BleepSound/ms20-vcf-simple/documentation/image/MS20-VCF-3D_bottom.png

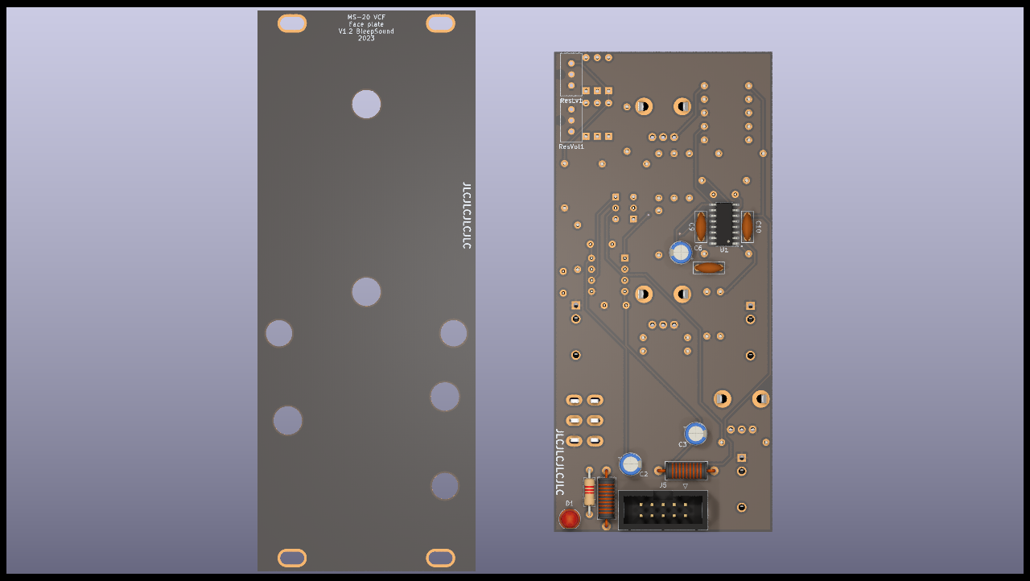
documentation/image/MS20-VCF-3D_bottom.png
