BleepSound/ms20-vcf-simple/documentation/image/MS20-VCF-3D_top30deg.png

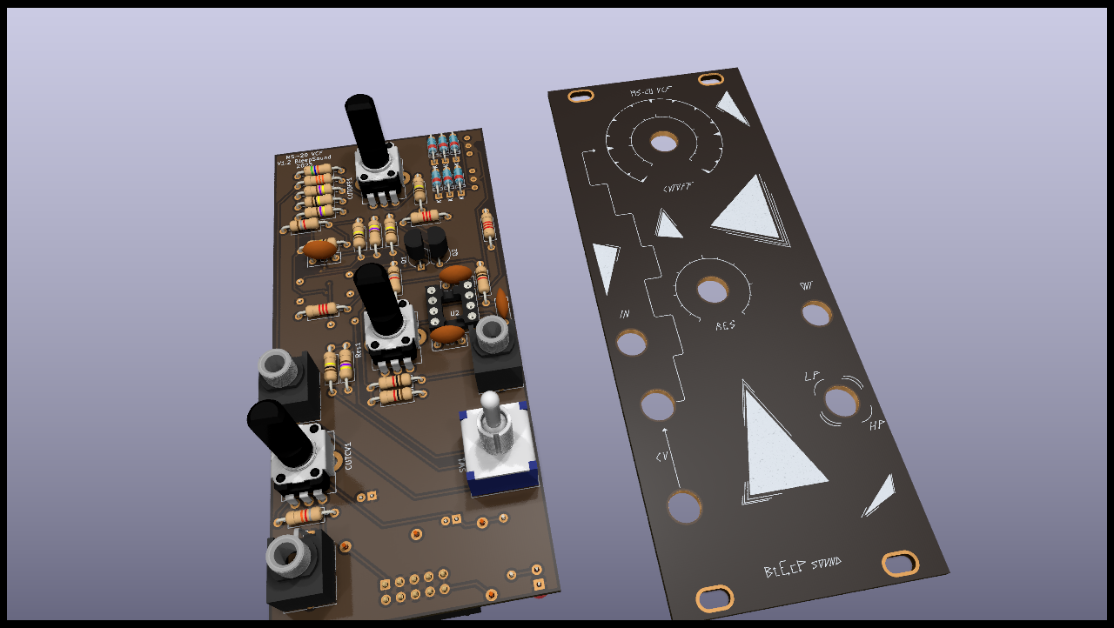
documentation/image/MS20-VCF-3D_top30deg.png
