BleepSound/ms20-vcf-simple/documentation/image/MS20-VCF-top.png

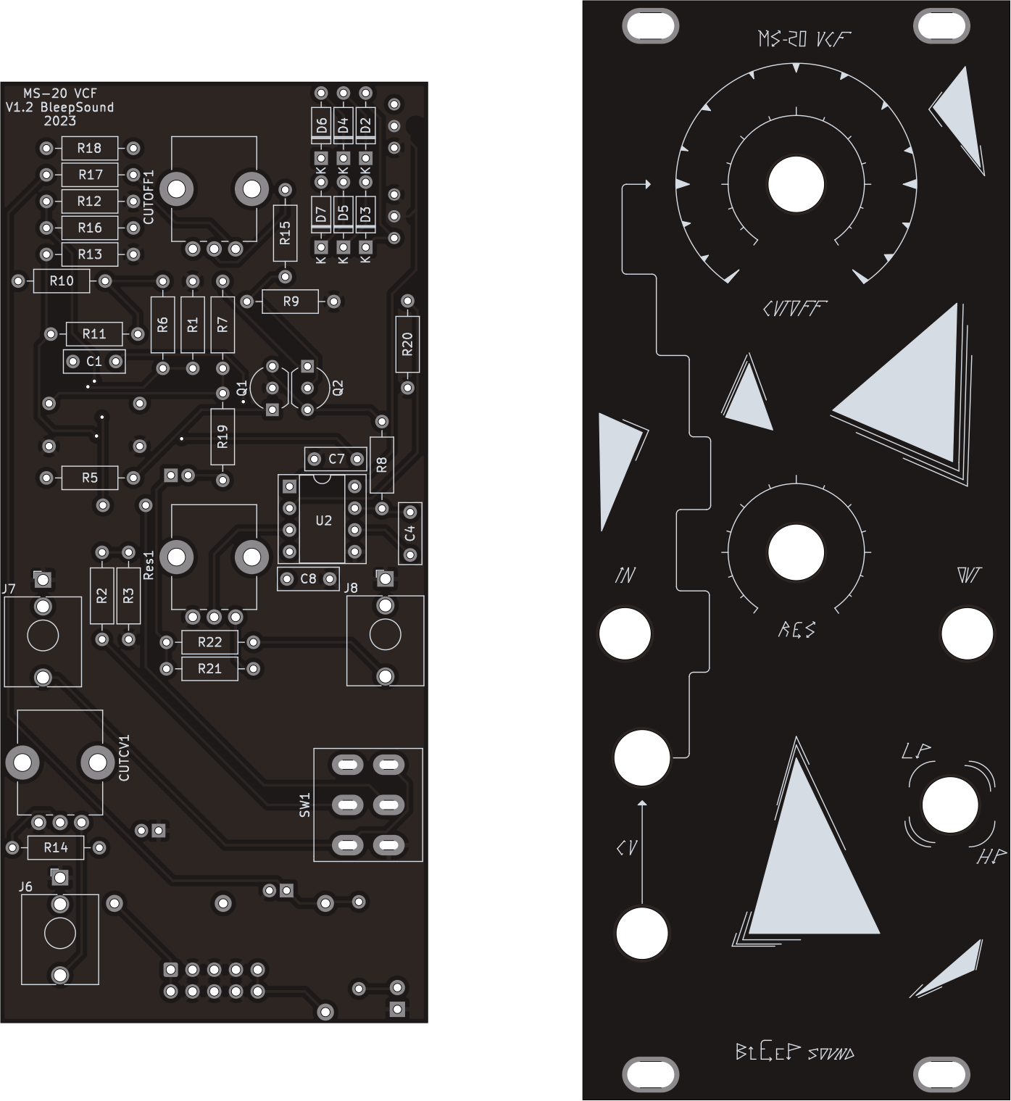
documentation/image/MS20-VCF-top.png
